PolLopezPena/MechanicalTurk/Face/Mouth/patterns.h

#ifndef PATTERNS_H
#define PATTERNS_H

// Dimensiones de la matriz NeoPixel
#define MATRIX_WIDTH 32
#define MATRIX_HEIGHT 8

// Define el número de patrones
#define NUM_PATTERNS 5

const uint8_t pattern1[MATRIX_HEIGHT][(MATRIX_WIDTH + 7) / 8] = {
  {0b00000000, 0b11111111, 0b11111111, 0b00000000},
  {0b00000000, 0b10010010, 0b01001001, 0b00000000},
  {0b00000000, 0b10010010, 0b01001001, 0b00000000},
  {0b00000000, 0b01010010, 0b01001010, 0b00000000},
  {0b00000000, 0b01010010, 0b01001010, 0b00000000},
  {0b00000000, 0b00110010, 0b01001100, 0b00000000},
  {0b00000000, 0b00010010, 0b01001000, 0b00000000},
  {0b00000000, 0b00001111, 0b11110000, 0b00000000}
};

const uint8_t pattern2[MATRIX_HEIGHT][(MATRIX_WIDTH + 7) / 8] = {
  {0b00000000, 0b11111111, 0b11111111, 0b00000000},
  {0b00000000, 0b10000000, 0b00000001, 0b00000000},
  {0b00000000, 0b10000000, 0b00000001, 0b00000000},
  {0b00000000, 0b01000000, 0b00000010, 0b00000000},
  {0b00000000, 0b01000000, 0b00000010, 0b00000000},
  {0b00000000, 0b00100000, 0b00000100, 0b00000000},
  {0b00000000, 0b00010000, 0b00001000, 0b00000000},
  {0b00000000, 0b00001111, 0b11110000, 0b00000000}
};

const uint8_t pattern3[MATRIX_HEIGHT][(MATRIX_WIDTH + 7) / 8] = {
  {0b00000000, 0b00001111, 0b11110000, 0b00000000},
  {0b00000000, 0b00010010, 0b01001000, 0b00000000},
  {0b00000000, 0b00110010, 0b01001100, 0b00000000},
  {0b00000000, 0b01010010, 0b01001010, 0b00000000},
  {0b00000000, 0b01010010, 0b01001010, 0b00000000},
  {0b00000000, 0b10010010, 0b01001001, 0b00000000},
  {0b00000000, 0b10010010, 0b01001001, 0b00000000},
  {0b00000000, 0b11111111, 0b11111111, 0b00000000}
};

const uint8_t pattern4[MATRIX_HEIGHT][(MATRIX_WIDTH + 7) / 8] = {
  {0b00000000, 0b00001111, 0b11110000, 0b00000000},
  {0b00000000, 0b00010000, 0b00001000, 0b00000000},
  {0b00000000, 0b00100000, 0b00000100, 0b00000000},
  {0b00000000, 0b01000000, 0b00000010, 0b00000000},
  {0b00000000, 0b01000000, 0b00000010, 0b00000000},
  {0b00000000, 0b10000000, 0b00000001, 0b00000000},
  {0b00000000, 0b10000000, 0b00000001, 0b00000000},
  {0b00000000, 0b11111111, 0b11111111, 0b00000000}
};

const uint8_t pattern5[MATRIX_HEIGHT][(MATRIX_WIDTH + 7) / 8] = {
  {0b00000000, 0b00000000, 0b00000000, 0b00000000},
  {0b00000000, 0b00000000, 0b00000000, 0b00000000},
  {0b00000000, 0b00000000, 0b00000000, 0b00000000},
  {0b00000000, 0b00111111, 0b11111100, 0b00000000},
  {0b00000000, 0b01000000, 0b00000010, 0b00000000},
  {0b00000000, 0b00000000, 0b00000000, 0b00000000},
  {0b00000000, 0b00000000, 0b00000000, 0b00000000},
  {0b00000000, 0b00000000, 0b00000000, 0b00000000}
};

#endif
